bebert0x42/Spool_Measurer/Screenshot/Bobine In 1.png

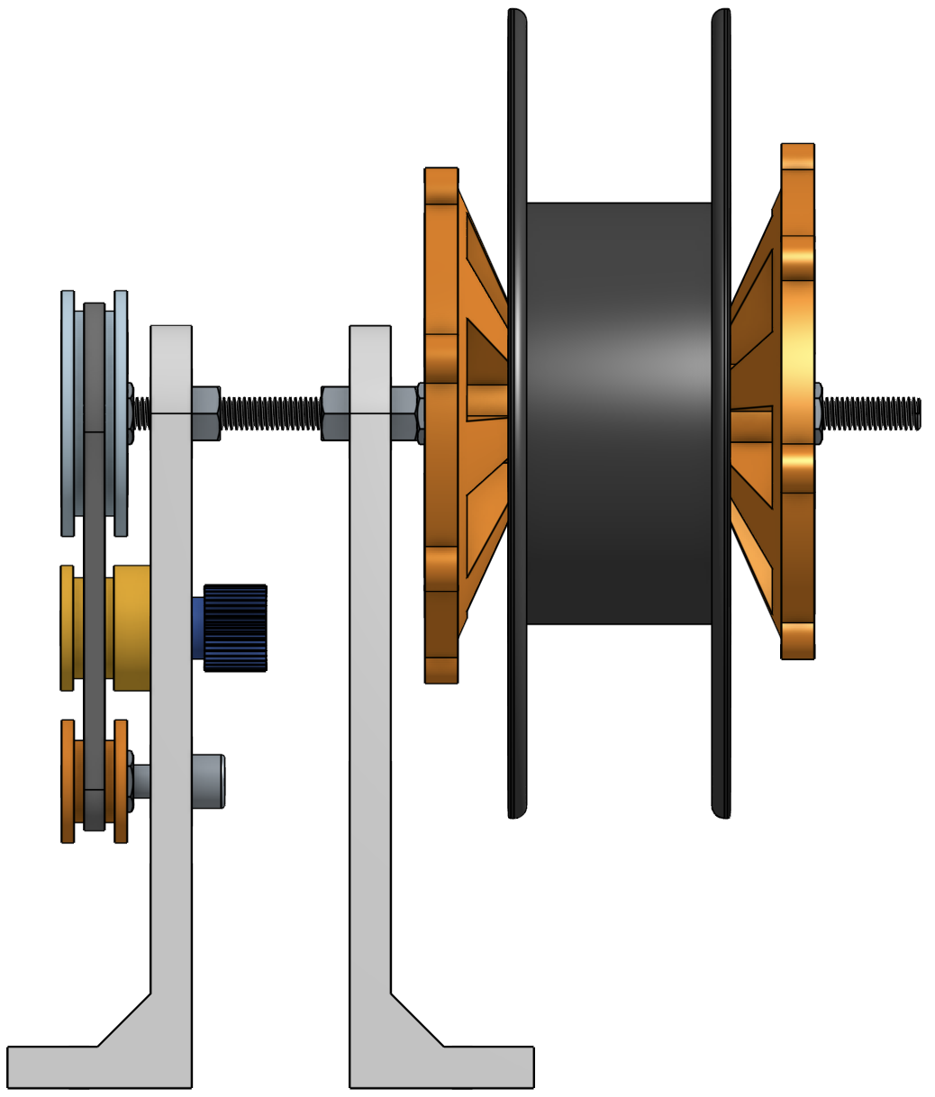
Screenshot/Bobine In 1.png
