bebert0x42/Spool_Measurer/Screenshot/Bobine In 2.png

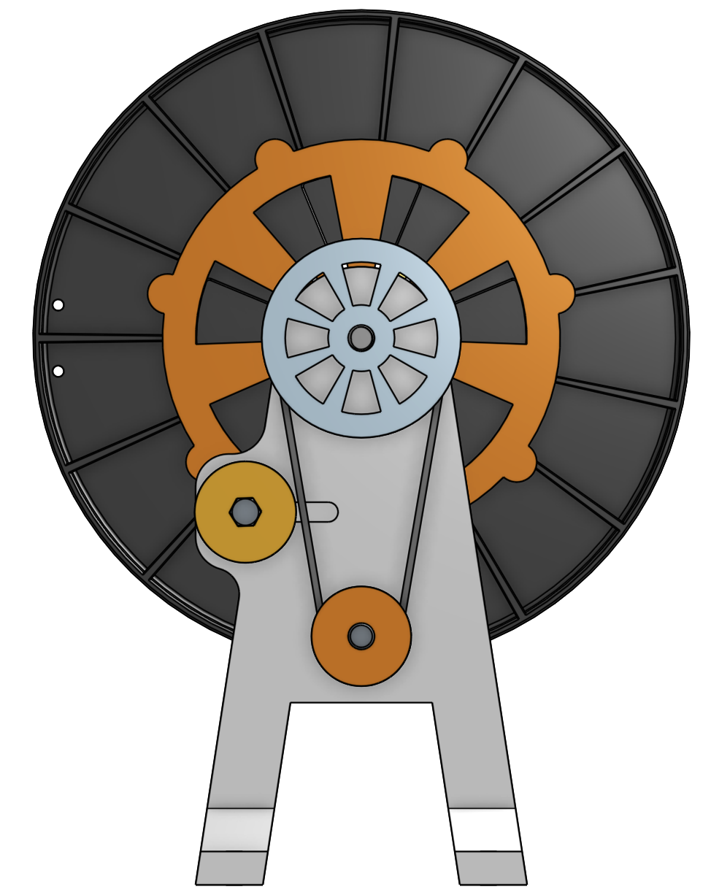
Screenshot/Bobine In 2.png
