bebert0x42/Spool_Measurer/Screenshot/Bobine In 3.png

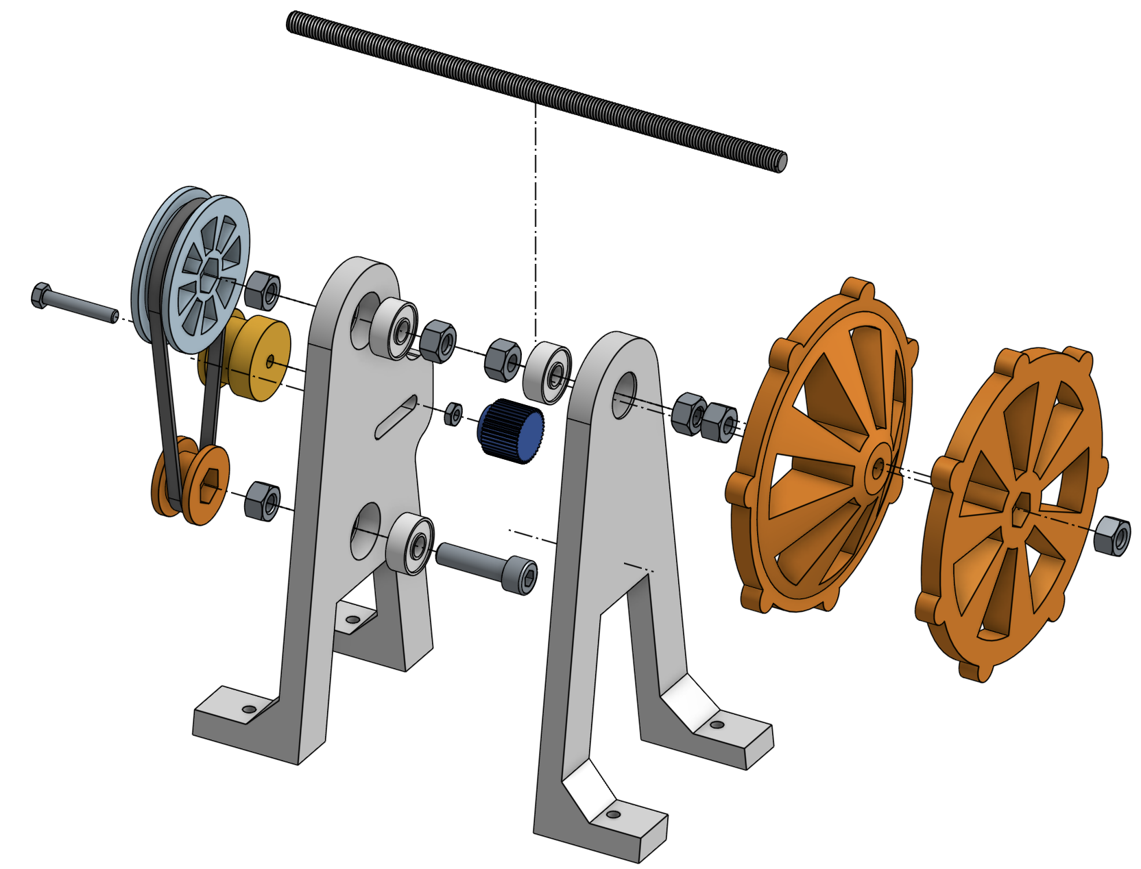
Screenshot/Bobine In 3.png
