bebert0x42/Spool_Measurer/Screenshot/Bobine Out 2.png

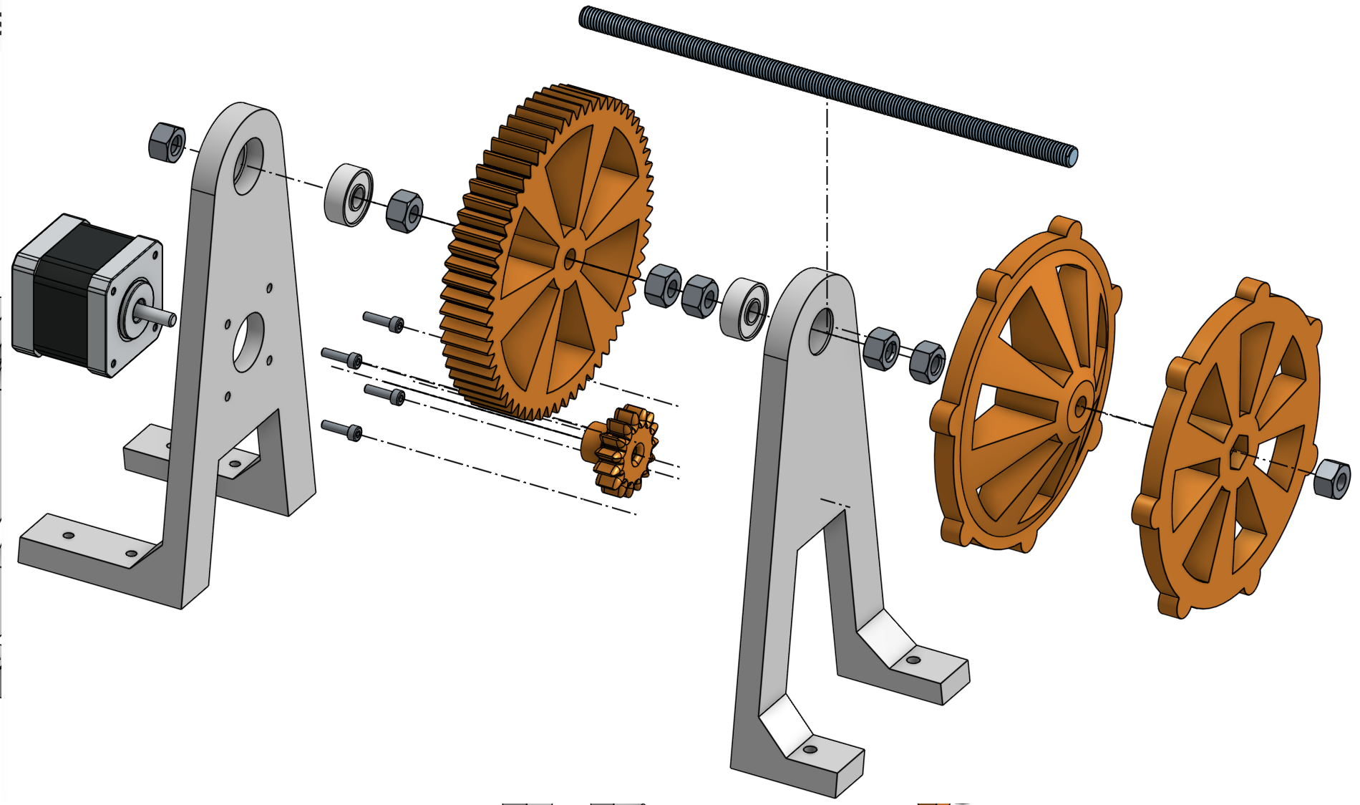
Screenshot/Bobine Out 2.png
