bebert0x42/Spool_Measurer/Screenshot/Box 1.png

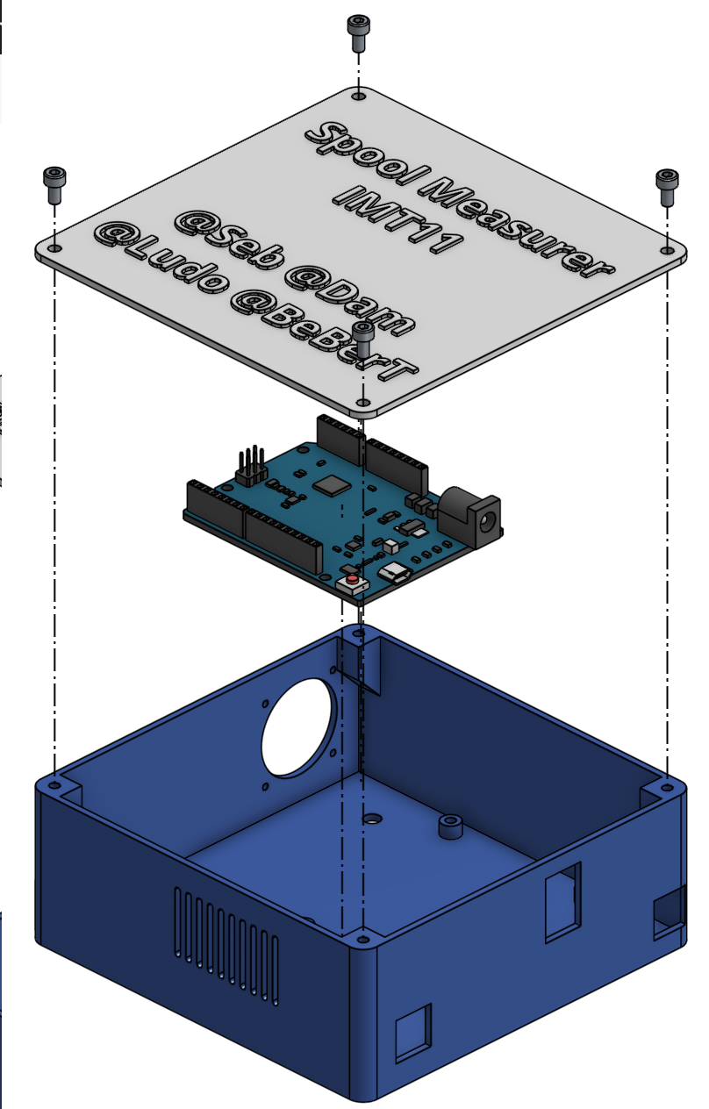
Screenshot/Box 1.png
