bebert0x42/Spool_Measurer/Screenshot/IHM 1.png

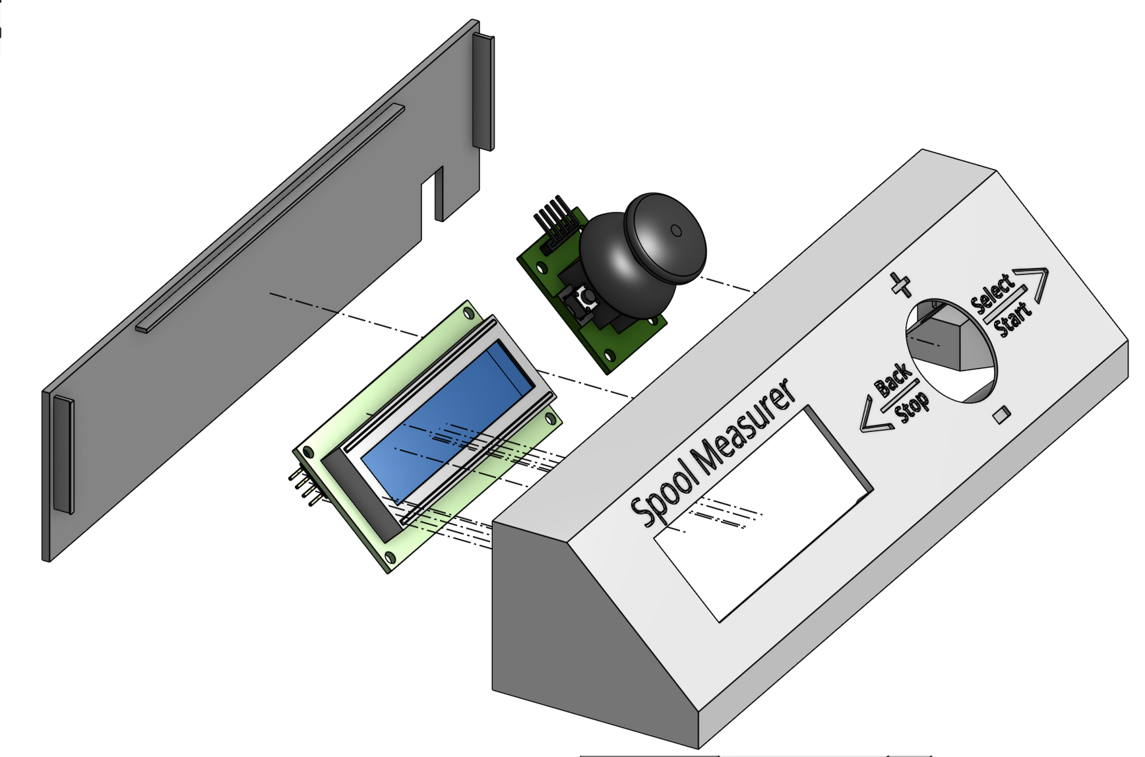
Screenshot/IHM 1.png
