bebert0x42/Spool_Measurer/Screenshot/Main 1.png

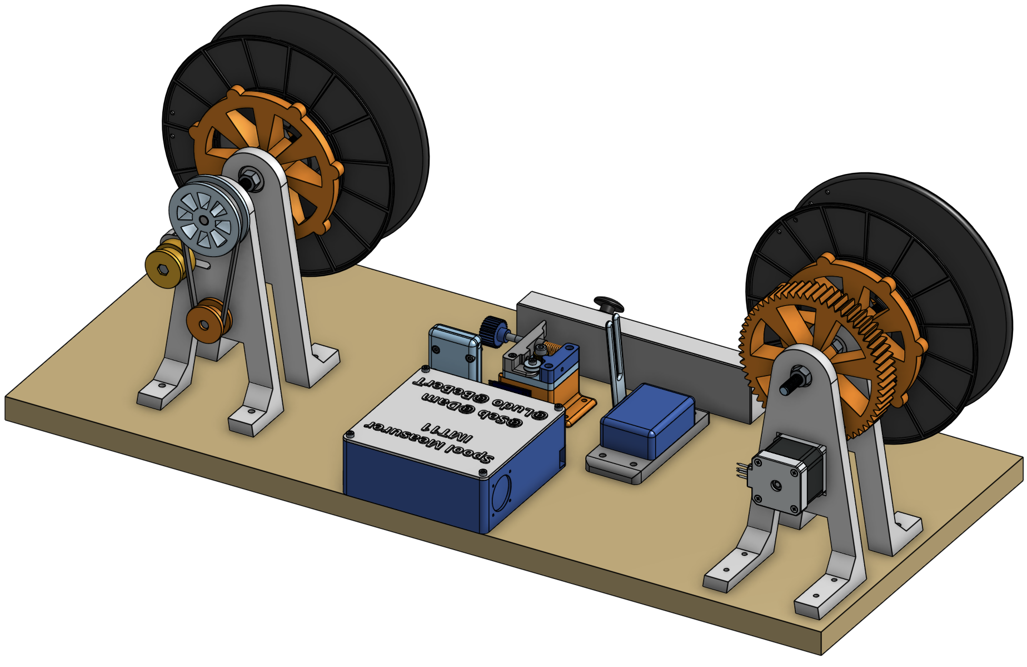
Screenshot/Main 1.png
