bebert0x42/Spool_Measurer/Screenshot/Main 2.png

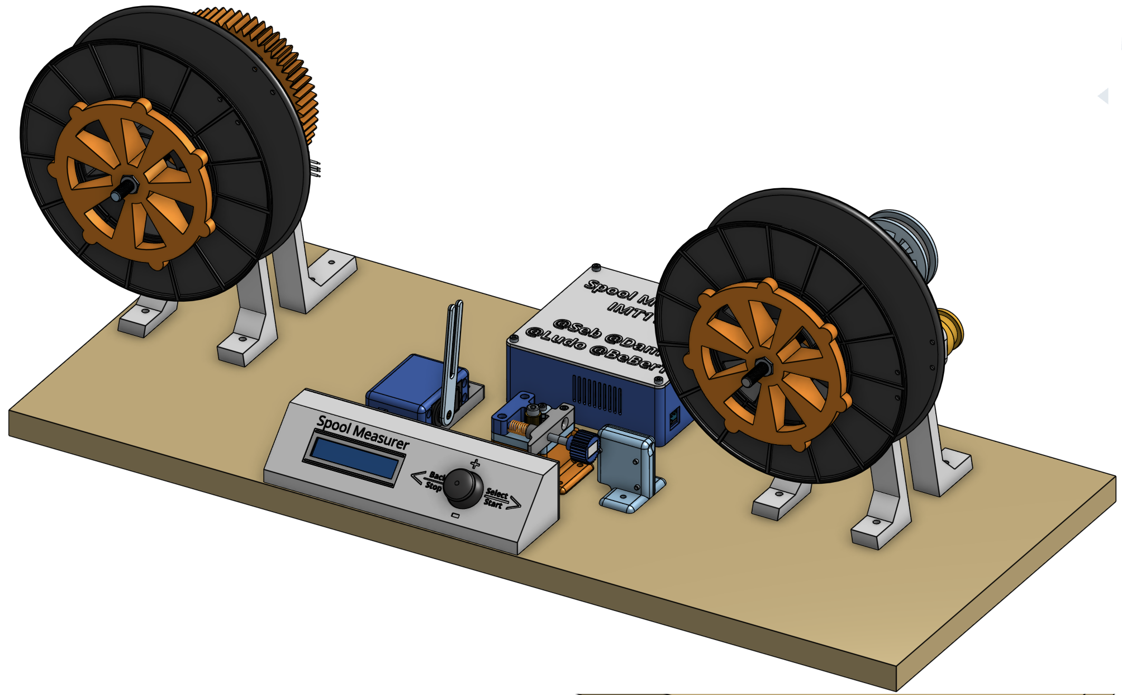
Screenshot/Main 2.png
