bebert0x42/Spool_Measurer/Screenshot/Main 4.png

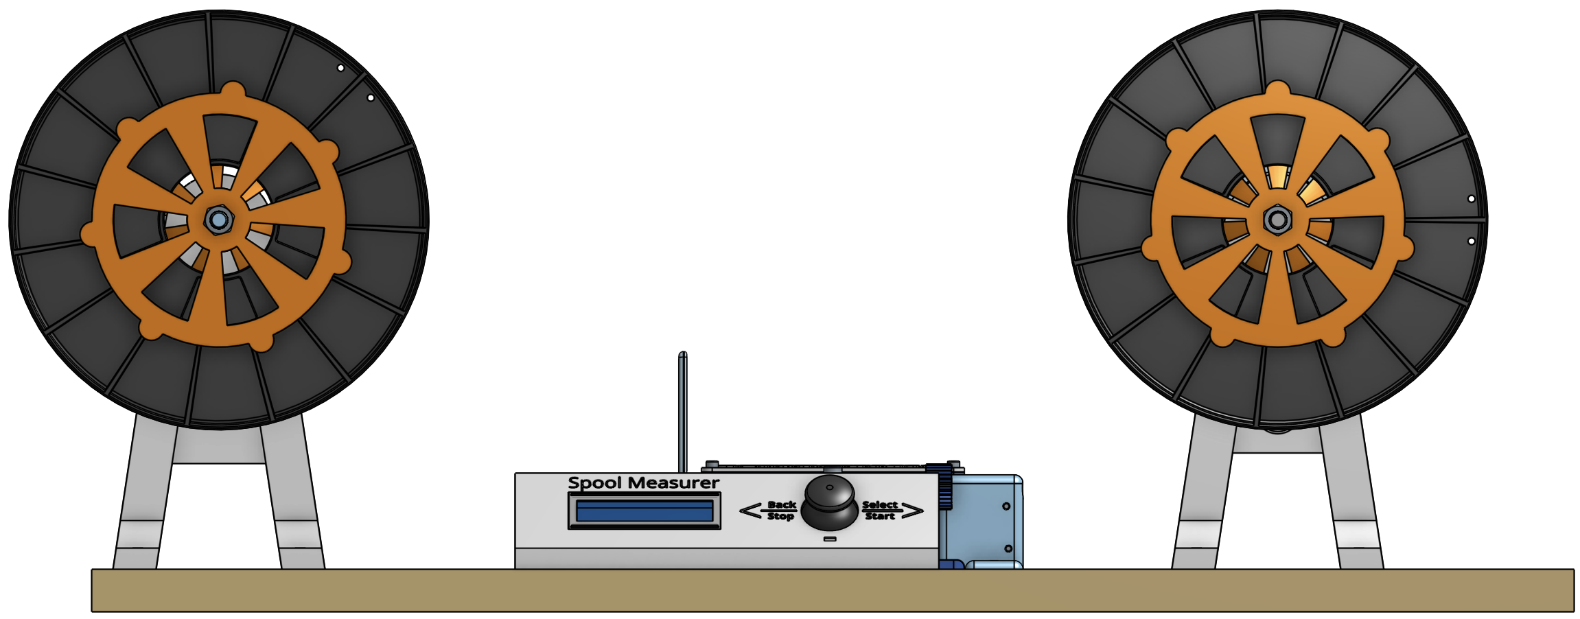
Screenshot/Main 4.png
