bebert0x42/Spool_Measurer/Screenshot/Schéma electronique PIC V3_bb.png

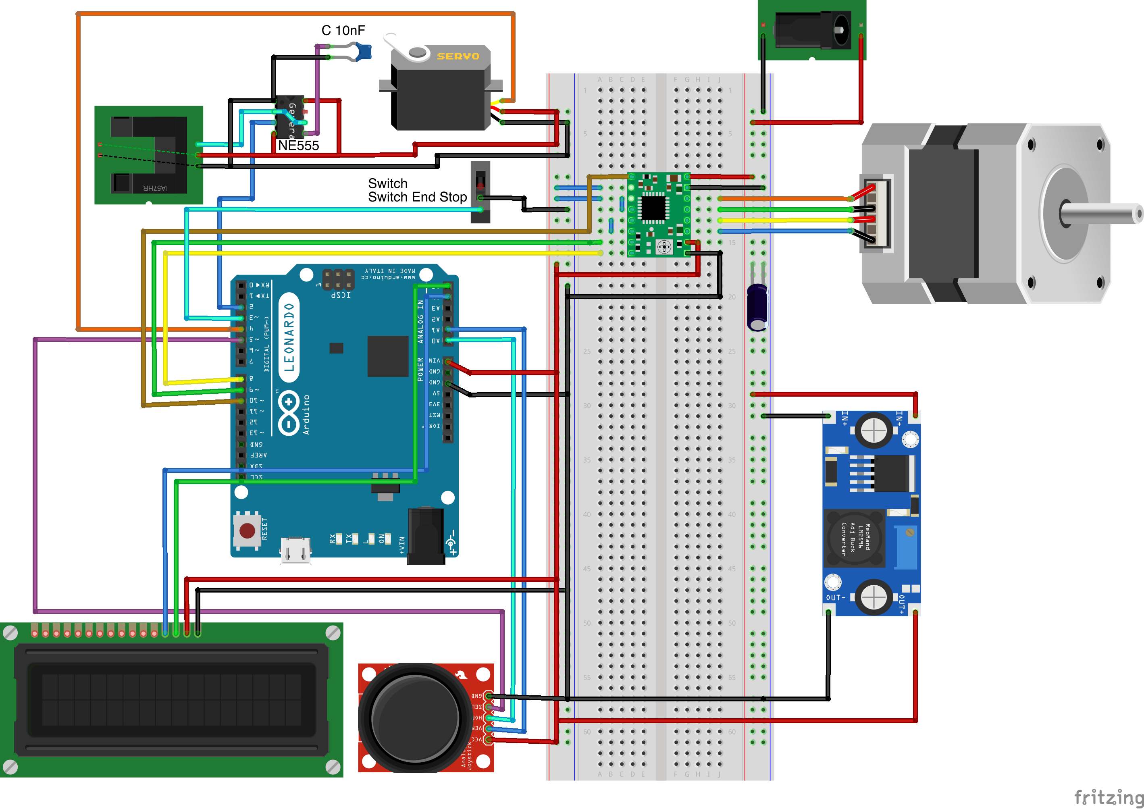
Screenshot/Schéma electronique PIC V3_bb.png
