bebert0x42/Spool_Measurer/Screenshot/Schéma electronique PIC V3_schéma.png

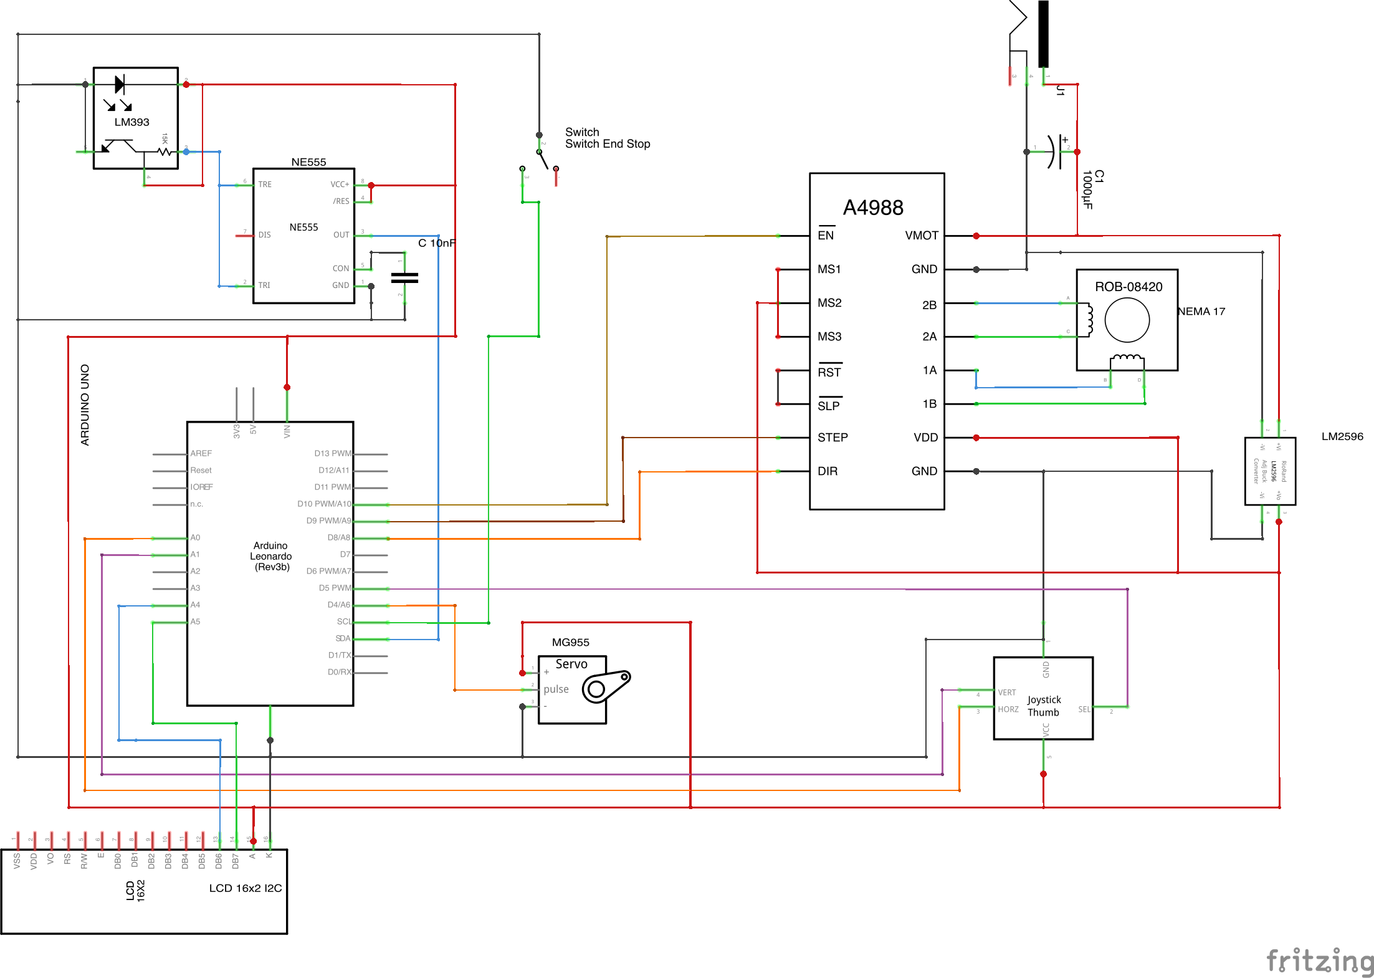
Screenshot/Schéma electronique PIC V3_schéma.png
