bebert0x42/Spool_Measurer/Screenshot/Sequence IHM.png

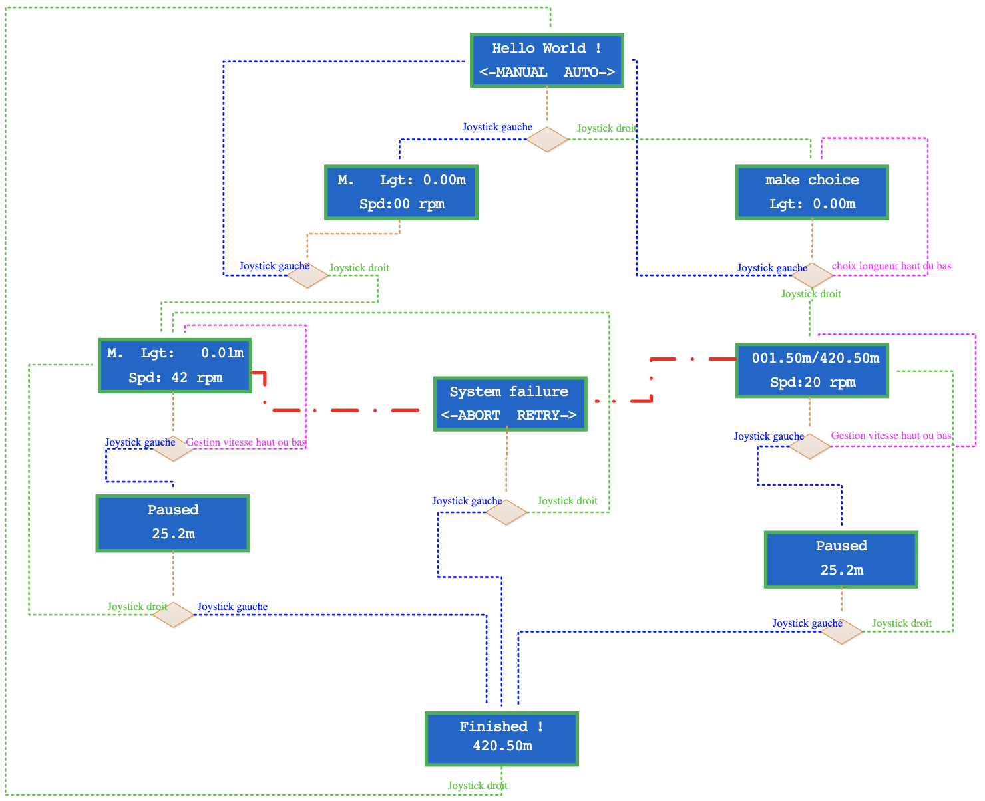
Screenshot/Sequence IHM.png
