bebert0x42/Spool_Measurer/Screenshot/Guide 1.png

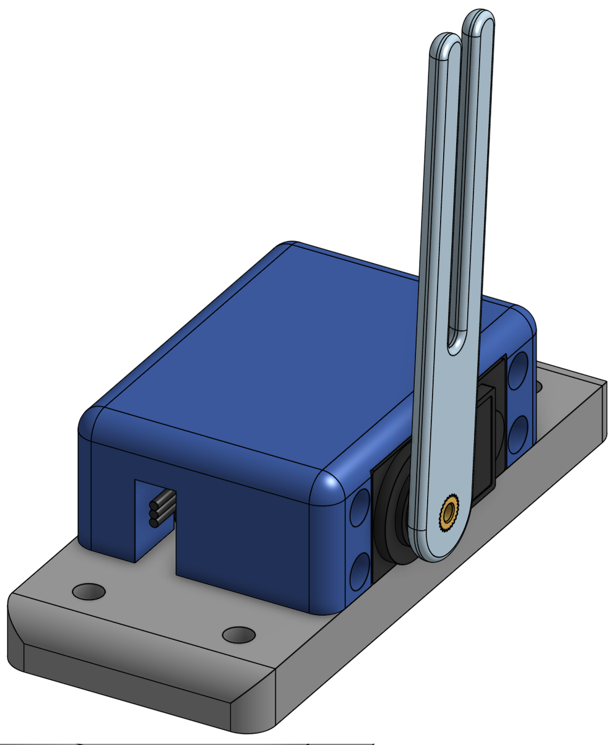
Screenshot/Guide 1.png
