bebert0x42/Spool_Measurer/Screenshot/Guide 2.png

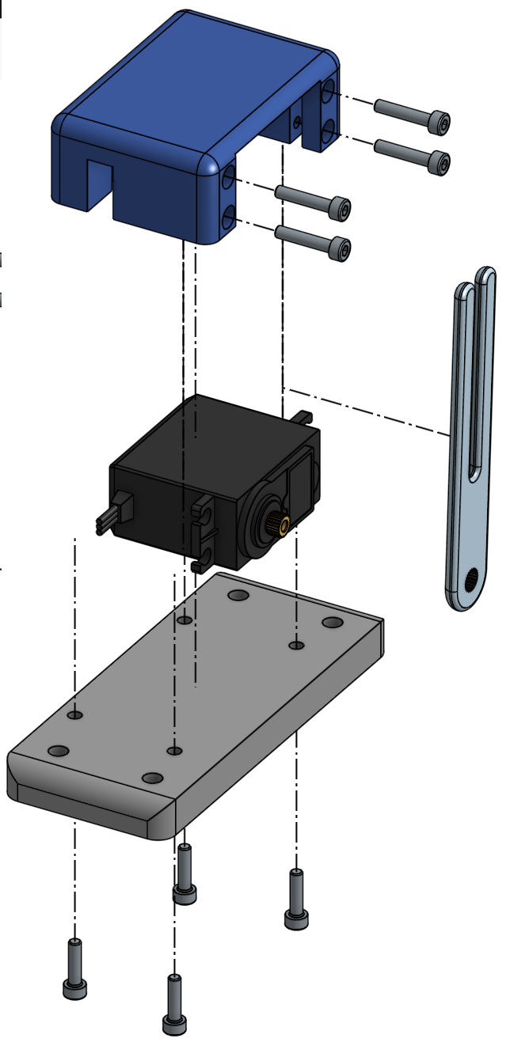
Screenshot/Guide 2.png
