bebert0x42/Spool_Measurer/Screenshot/Measurer 3.png

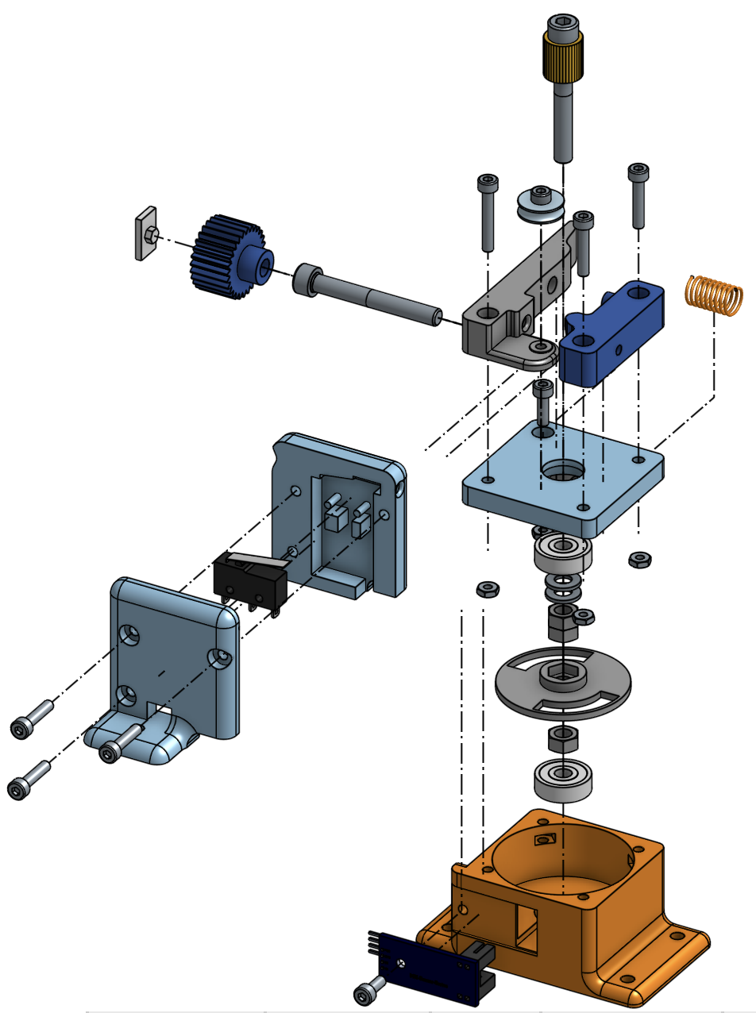
Screenshot/Measurer 3.png
